connected-digital-energy-meter/cdem_docs/docs/08_working/README.md

# Running

UNDER CONSTRUCTION

Once your Digital Energy Meter device is powered it will start booting.

## Indicator led's

There are two indicator led's that tell you the status of your Digital Energy Meter device.

### Communication led

<!-- TODO - place here animated gif's to explane the device status indication with the COM led's. -->

### Data led

<!-- TODO - place here animated gif's to explane the device status indication with the DATA led's. -->

## Your device at work

Once your device has wifi connection and is connected to your MQTT broker it will periodicaly:
* read a datagram from the P1 port of your Fluvius Digital Meter
* validate the recieved datagram
* decode the datagram to actual data
* publish that data to your MQTT broker

## Resetting your device

In the unfortunate case the firmware of your Digital Energy Meter device  crashes or gets stuck, you can reset your device.
Place a thin but not sharp pin into the hole just beneath the VIVES logo and press gently.

Your device wil reboot.

Ofcourse you can also interupt the USB powersupply to do this.
