connected-digital-energy-meter/cdem_docs/assets/cdem_pcb_v4.png

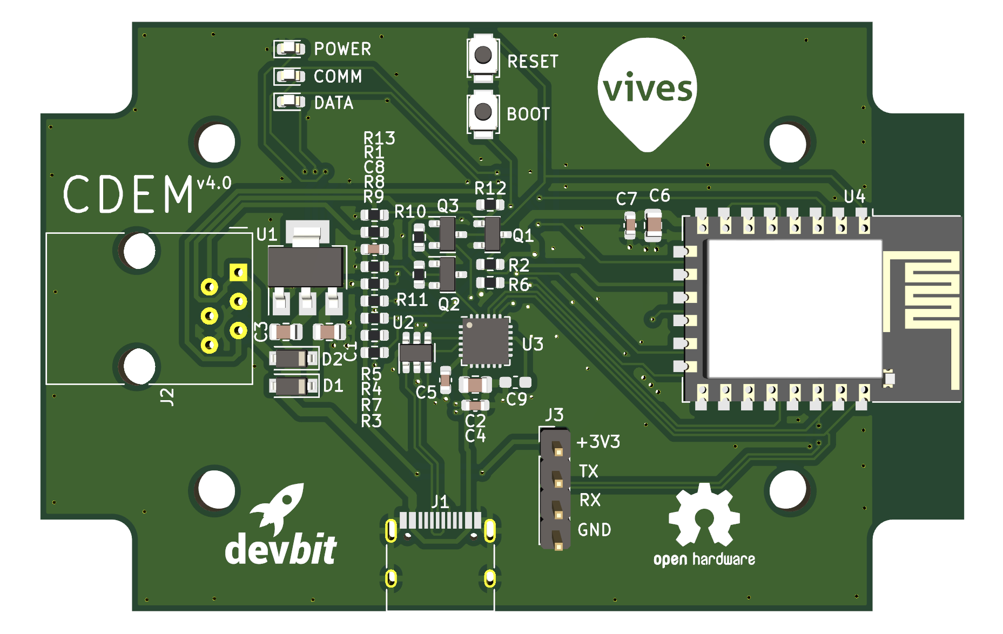
assets/cdem_pcb_v4.png
