connected-digital-energy-meter/cdem_docs/docs/02_hardware/images/pcb.jpg

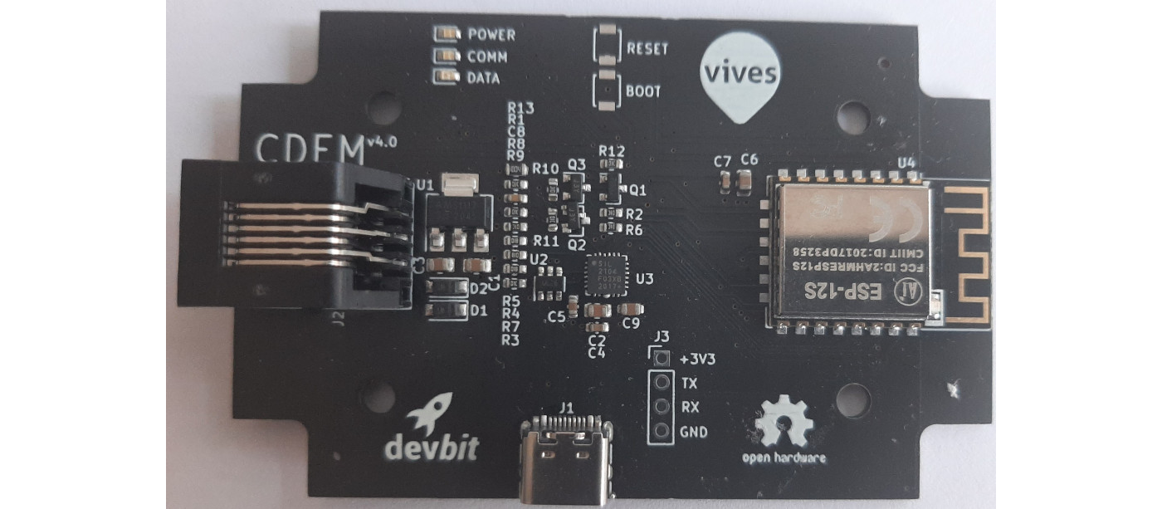
docs/02_hardware/images/pcb.jpg
