connected-digital-energy-meter/cdem_docs/docs/03_firmware/images/flash_firmware.jpg

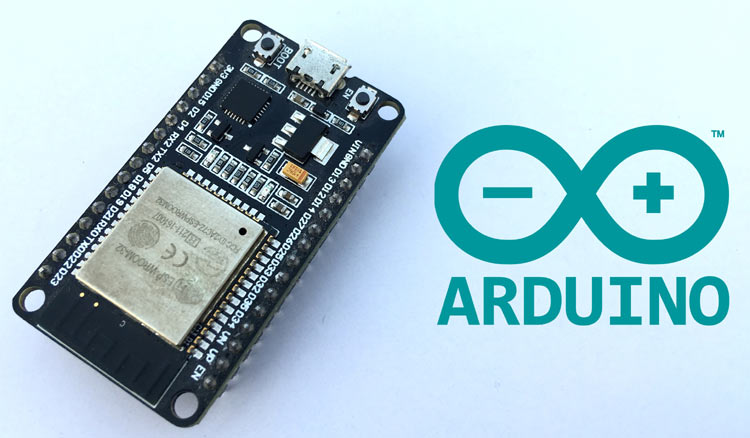
docs/03_firmware/images/flash_firmware.jpg
