connected-digital-energy-meter/cdem_docs/docs/05_connect/images/rj11.jpg

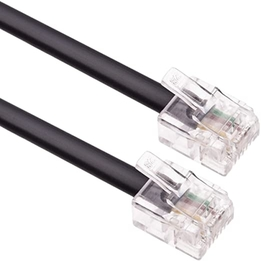
docs/05_connect/images/rj11.jpg
